thilaire/enterCode/photos/IMG_4238.JPG

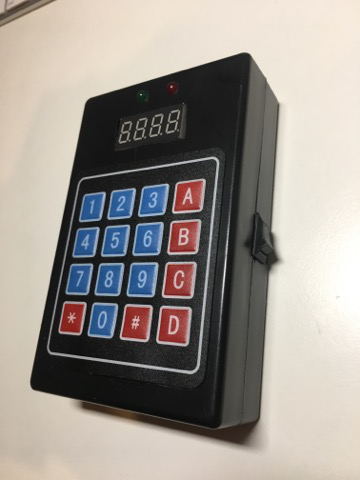
photos/IMG_4238.JPG
