thilaire/enterCode/photos/IMG_4239.JPG

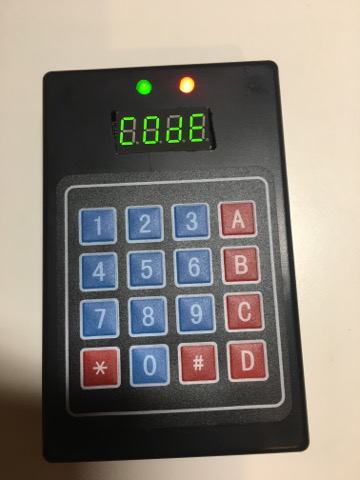
photos/IMG_4239.JPG
