thilaire/enterCode/photos/IMG_4240.JPG

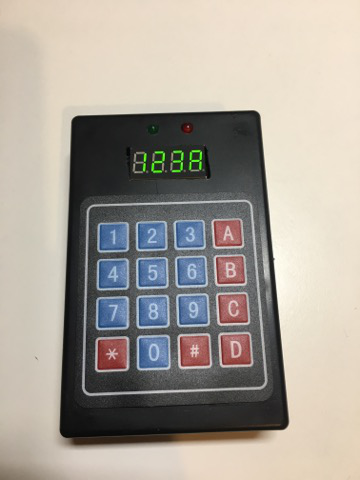
photos/IMG_4240.JPG
