thilaire/enterCode/photos/IMG_4241.JPG

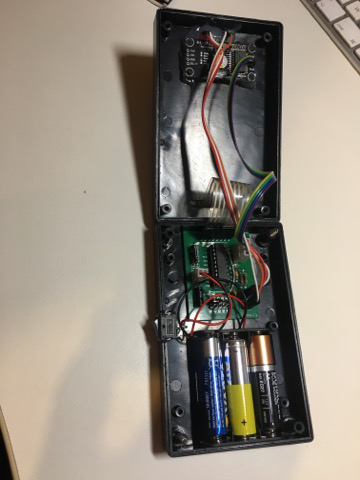
photos/IMG_4241.JPG
