thilaire/enterCode/photos/IMG_4242.JPG

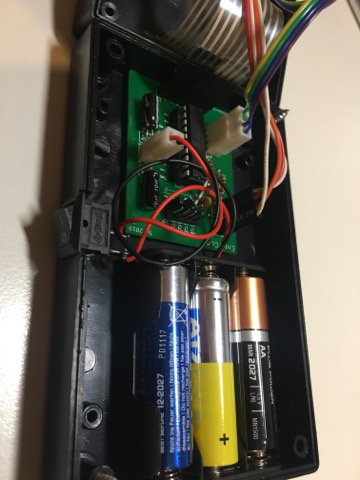
photos/IMG_4242.JPG
