thilaire/enterCode/photos/IMG_4243.JPG

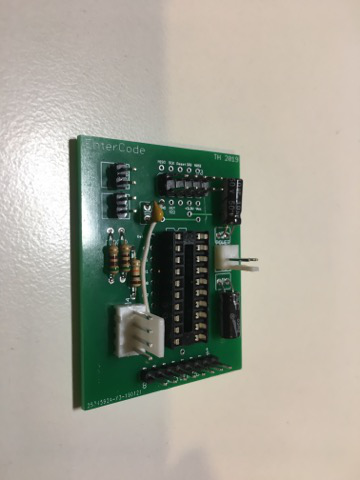
photos/IMG_4243.JPG
