thilaire/enterCode/photos/IMG_4244.JPG

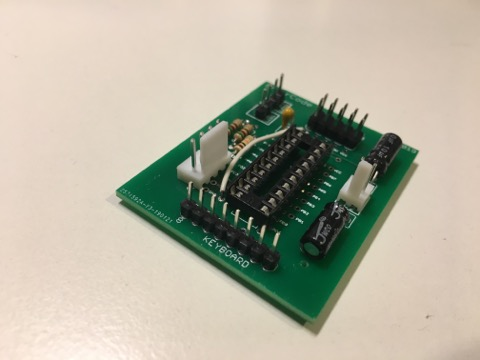
photos/IMG_4244.JPG
