thilaire/enterCode/photos/IMG_4245.JPG

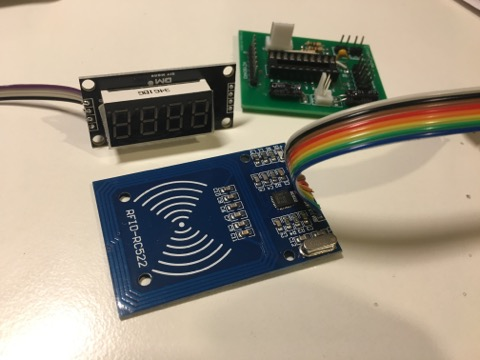
photos/IMG_4245.JPG
