thilaire/enterCode/photos/IMG_4246.JPG

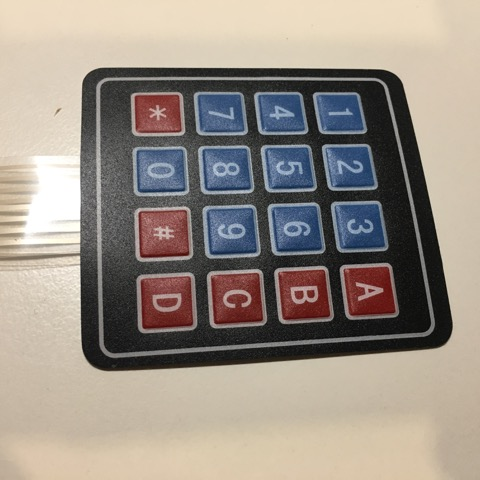
photos/IMG_4246.JPG
