thilaire/enterCode/photos/IMG_4247.JPG

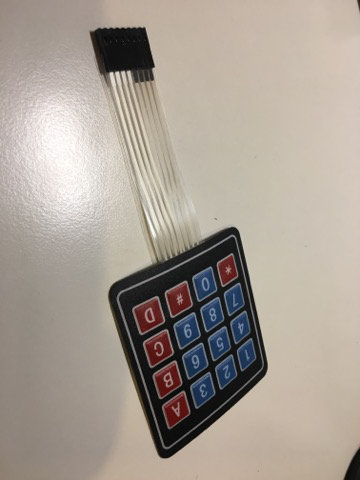
photos/IMG_4247.JPG
