thilaire/enterCode/src/enterCode.h

/*----------------------------------------------------------------------------

                          *============*
                          |            |
                          | enterCode  |
                          |            |
                          *============*


 Authors: T. HILAIRE
 Licence: GPL v3

 File: enterCode.h
       some constants


Copyright 2019 T. Hilaire

----------------------------------------------------------------------------*/


#ifndef ENTERCODE_ENTERCODE_H
#define ENTERCODE_ENTERCODE_H


/* maximum code size and number of codes (master + others)*/
#define CODE_SIZE	8
#define NB_CODES	4

/* keys */
#define KEY_AST		12
#define KEY_ZERO	13
#define KEY_SHARP 	14
#define NO_KEY		16


/* status */
#define ACCESS_MODE	0
#define MASTER_MODE 1



#endif //ENTERCODE_ENTERCODE_H
